s-light/cp_magic_painter/docu/prepare_images/gimp export BMP_settings.png

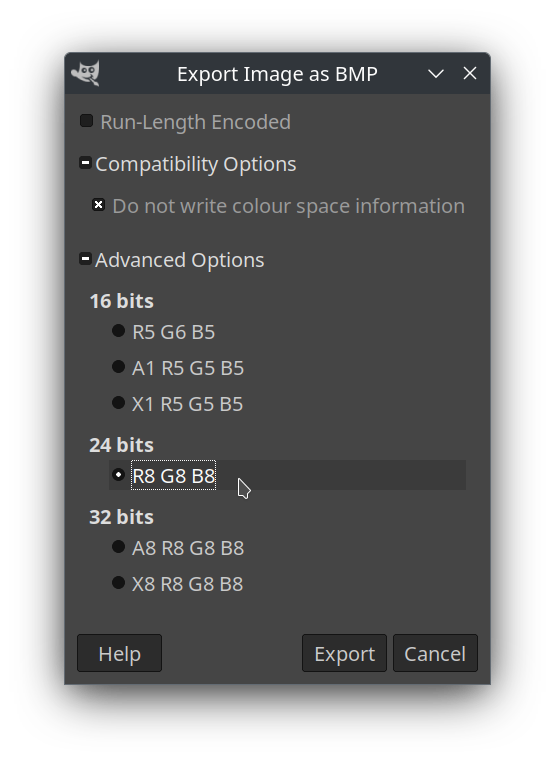
docu/prepare_images/gimp export BMP_settings.png
