s-light/cp_magic_painter/docu/prepare_images/openmoji.org candle PNG CtrClickCopy.png

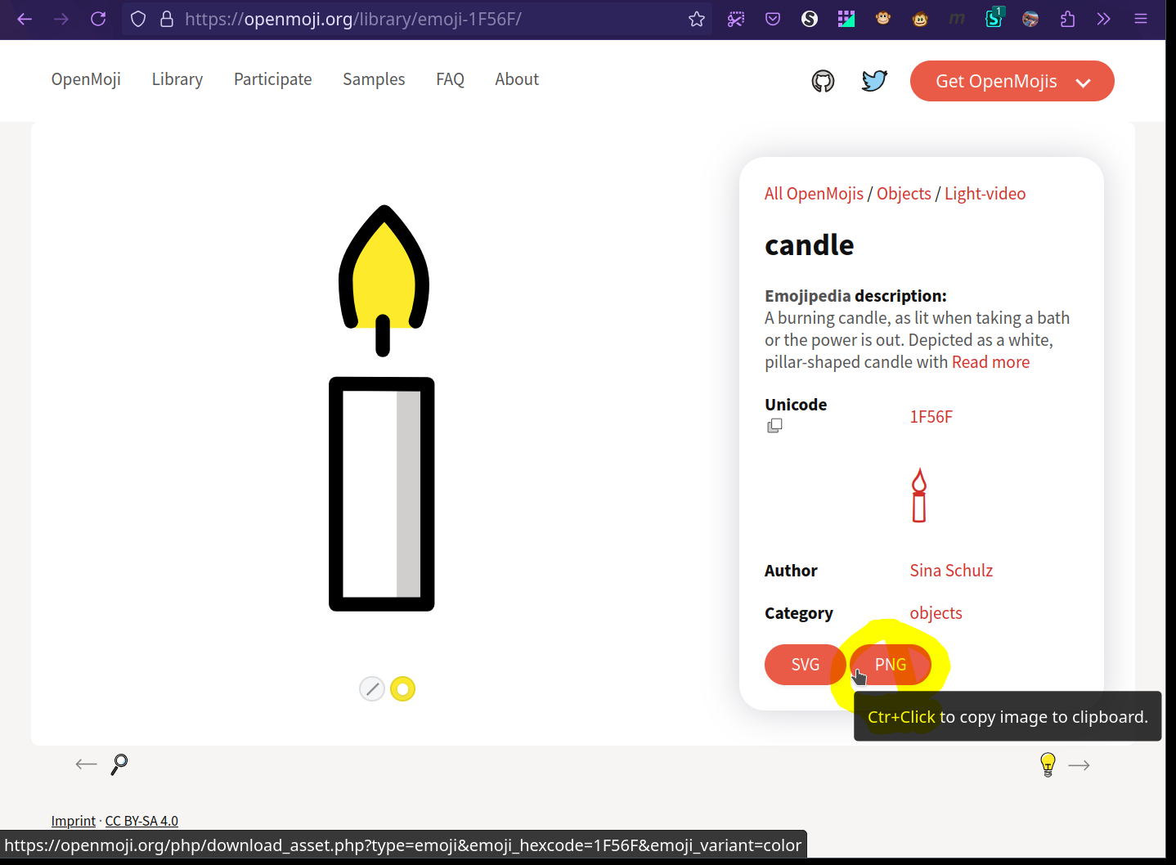
docu/prepare_images/openmoji.org candle PNG CtrClickCopy.png
