s-light/cp_magic_painter/docu/prepare_images/openmoji.org candle selected.png

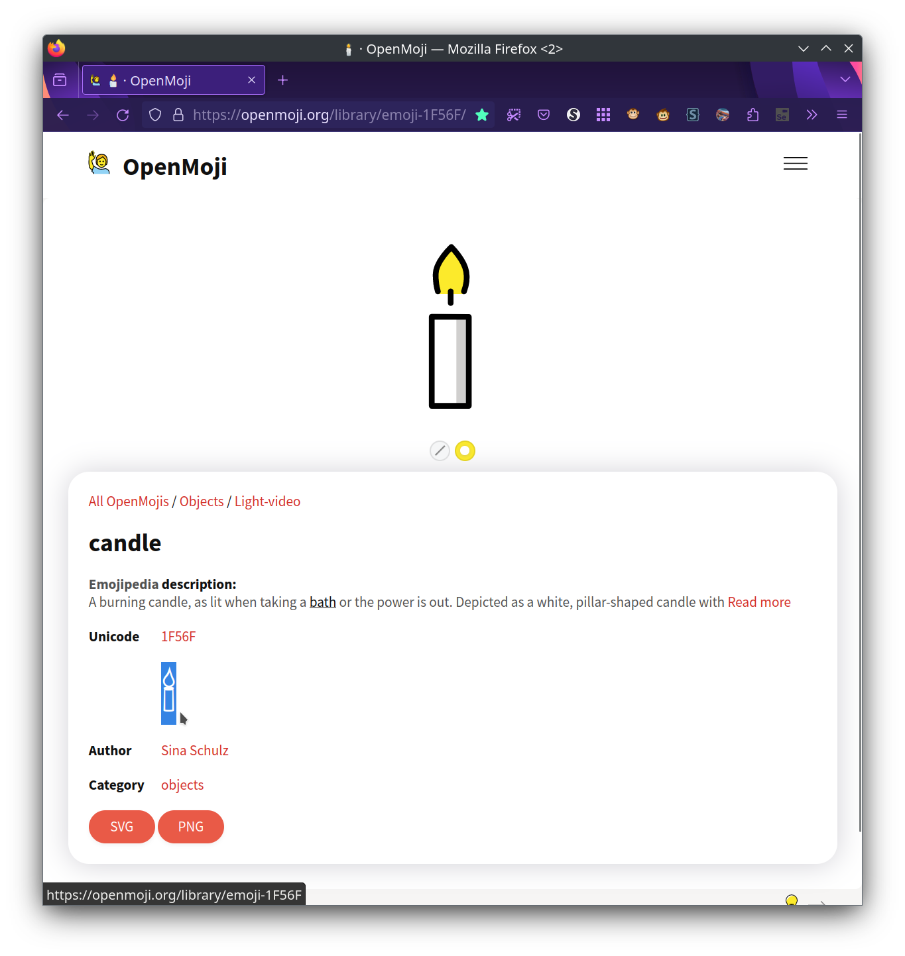
docu/prepare_images/openmoji.org candle selected.png
