s-light/cp_magic_painter/hw/pictures/20230304_v0/20230304_070338__hw.jpg

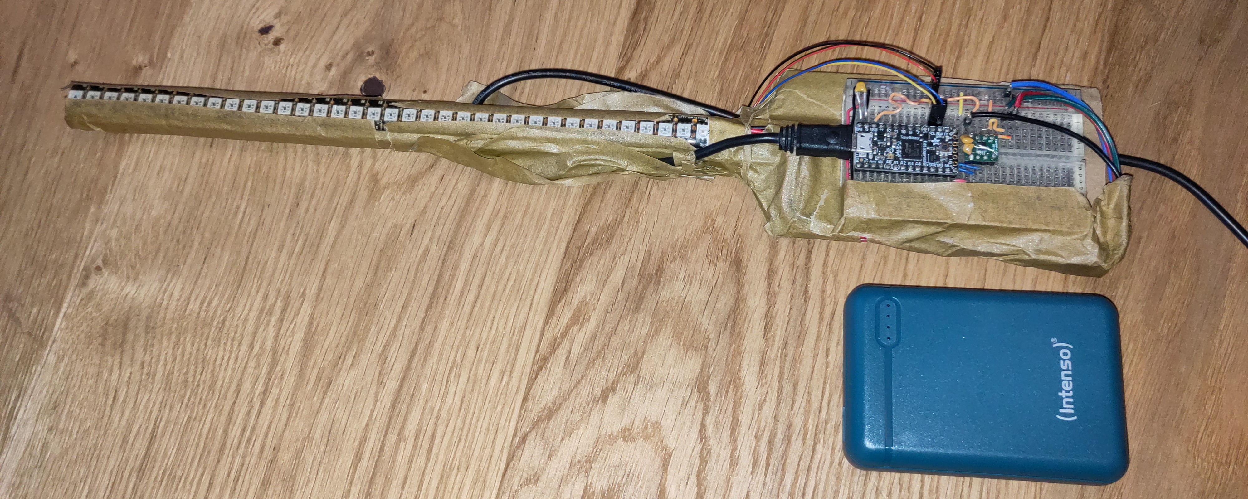
hw/pictures/20230304_v0/20230304_070338__hw.jpg
