s-light/cp_magic_painter/hw/pictures/20230304_v0/20230304_070426__crop_detail1.jpg

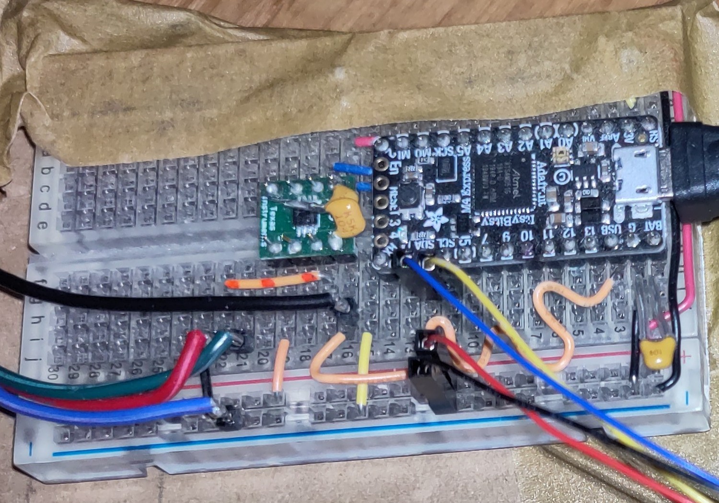
hw/pictures/20230304_v0/20230304_070426__crop_detail1.jpg
