s-light/cp_magic_painter/hw/pictures/20230304_v0/20230304_071858_DRO.jpg

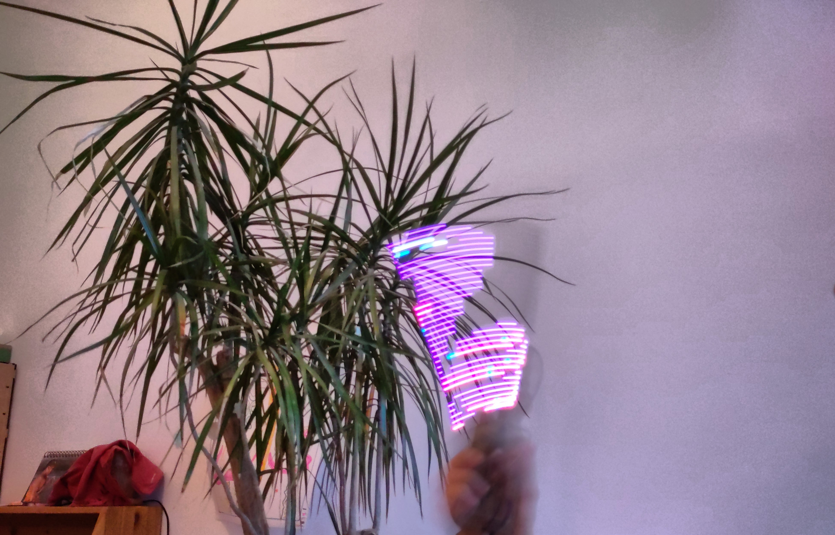
hw/pictures/20230304_v0/20230304_071858_DRO.jpg
