s-light/cp_magic_painter/hw/pictures/20230425_v1/20230422_122205.jpg

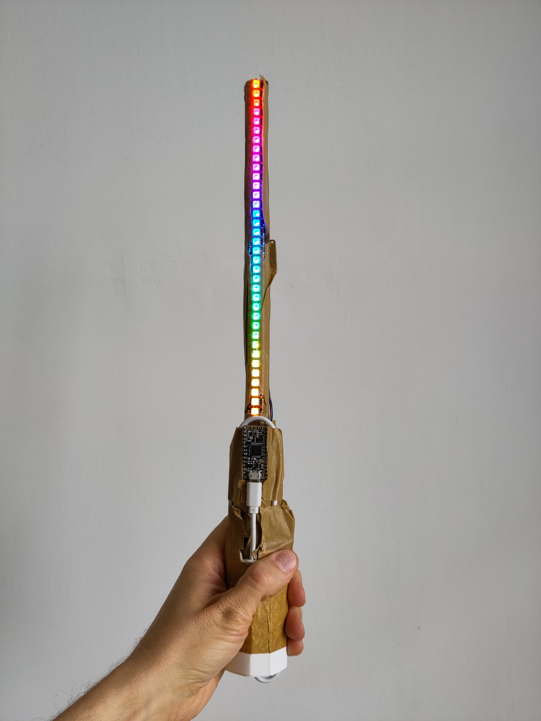
hw/pictures/20230425_v1/20230422_122205.jpg
