s-light/cp_magic_painter/hw/pictures/20230521_v2/20230628_010837.jpg

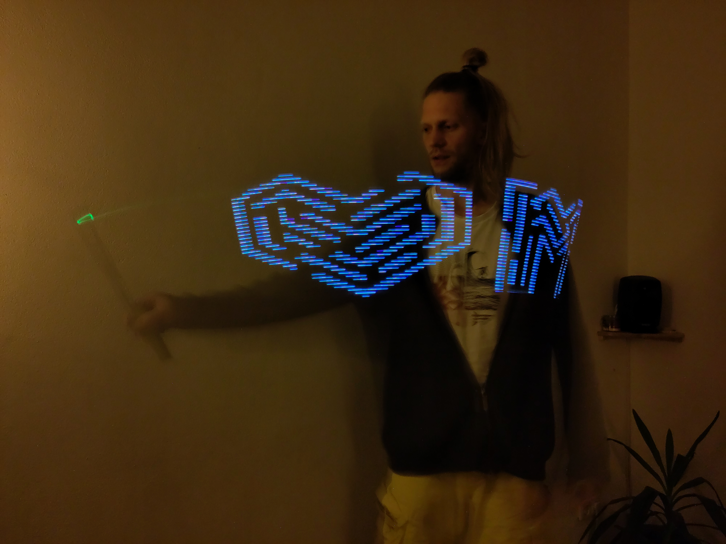
hw/pictures/20230521_v2/20230628_010837.jpg
