s-light/cp_magic_painter/hw/pictures/20230521_v2/20230628_011204.jpg

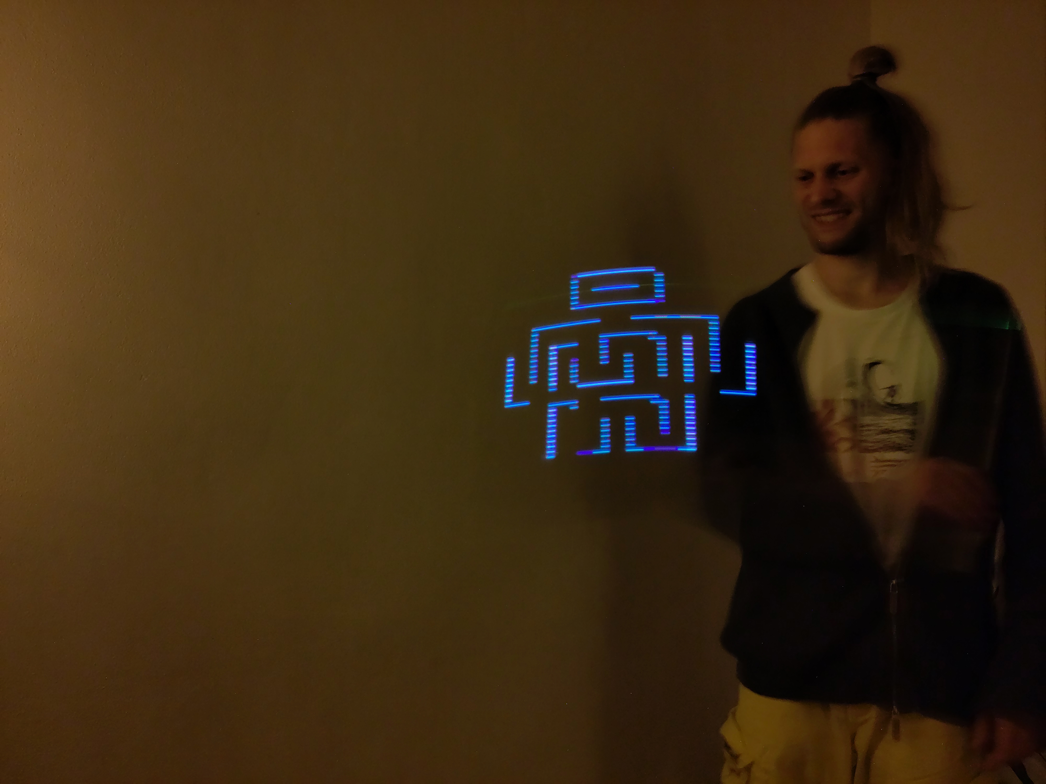
hw/pictures/20230521_v2/20230628_011204.jpg
