s-light/cp_magic_painter/hw/pictures/20230709 powerbank/20230709_113732.jpg

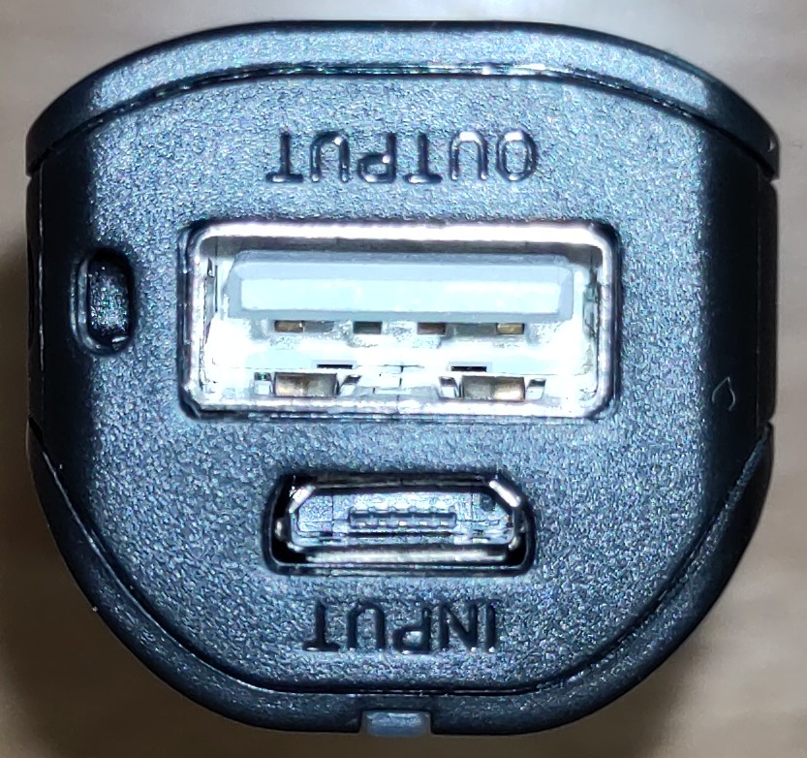
hw/pictures/20230709 powerbank/20230709_113732.jpg
