s-light/cp_magic_painter/hw/pictures/20230709 powerbank/20230709_113805.jpg

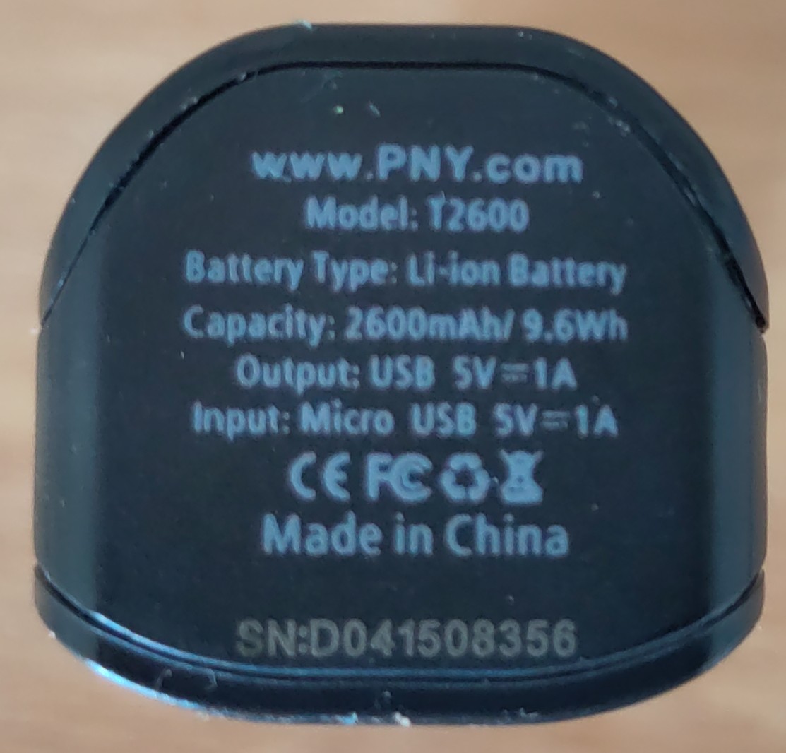
hw/pictures/20230709 powerbank/20230709_113805.jpg
