s-light/cp_magic_painter/hw/pictures/20230709 powerbank/20230709_114218.jpg

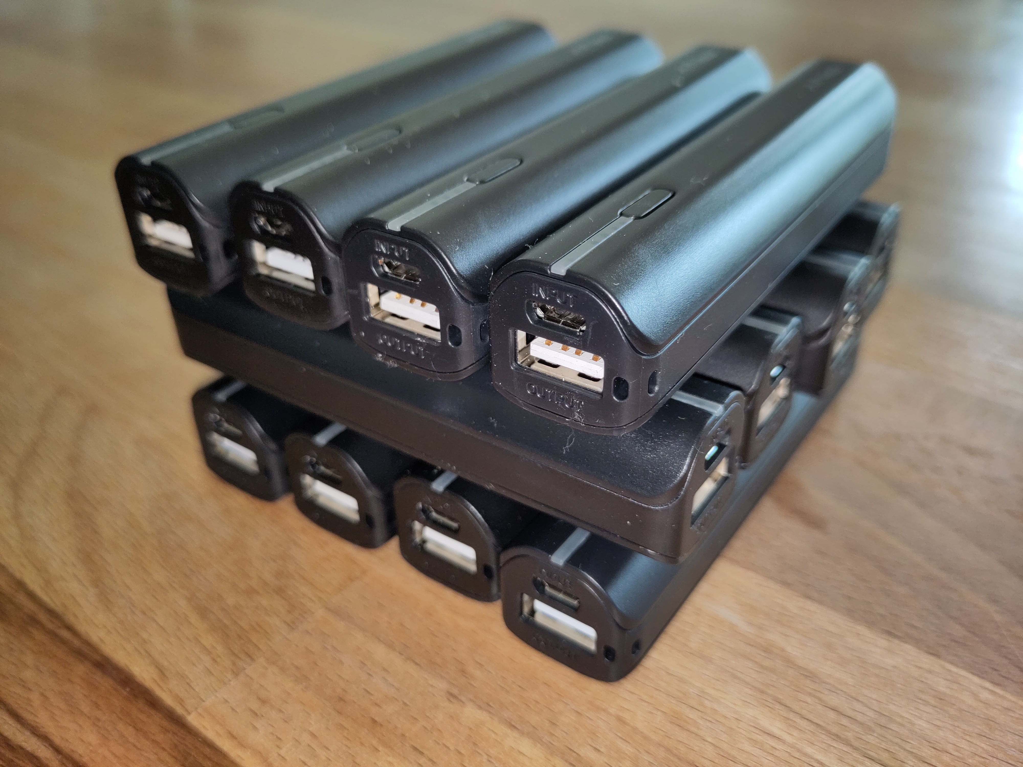
hw/pictures/20230709 powerbank/20230709_114218.jpg
