s-light/cp_magic_painter/hw/pictures/20230709 powerbank/20230726_093031.jpg

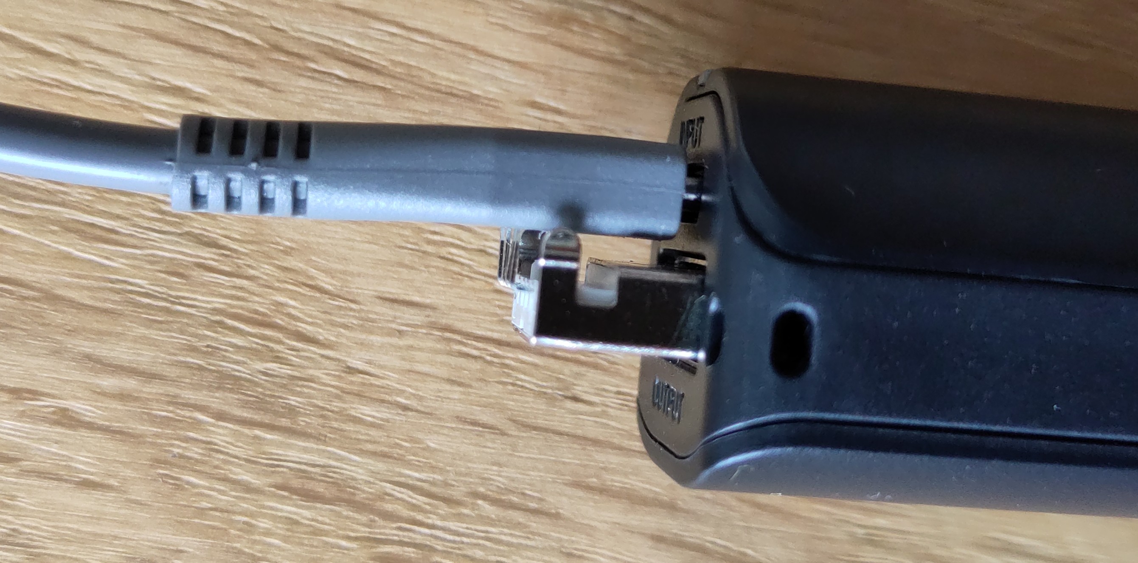
hw/pictures/20230709 powerbank/20230726_093031.jpg
