s-light/cp_magic_painter/hw/shrinktube_check.png

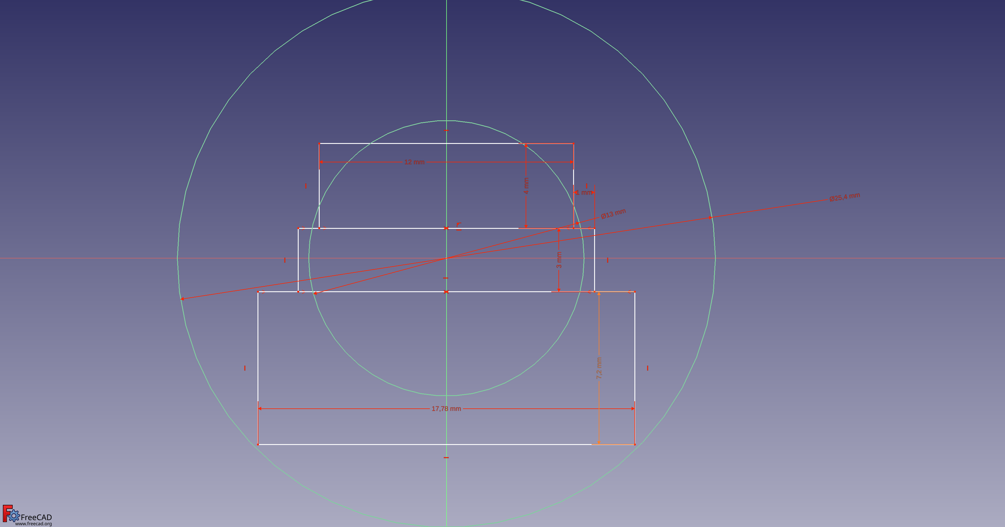
hw/shrinktube_check.png
