s-light/cp_magic_painter/hw/case/led_strip.FCStd

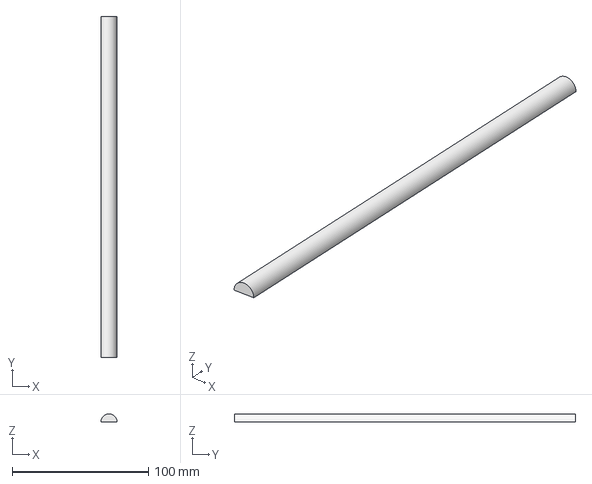
[picture p47: CAD file, 2023-09-12]
hw/case/led_strip.FCStd
12.0 x 250.0 x 6.00 mm
