s-light/cp_magic_painter/hw/case/LIS3DH.FCStd

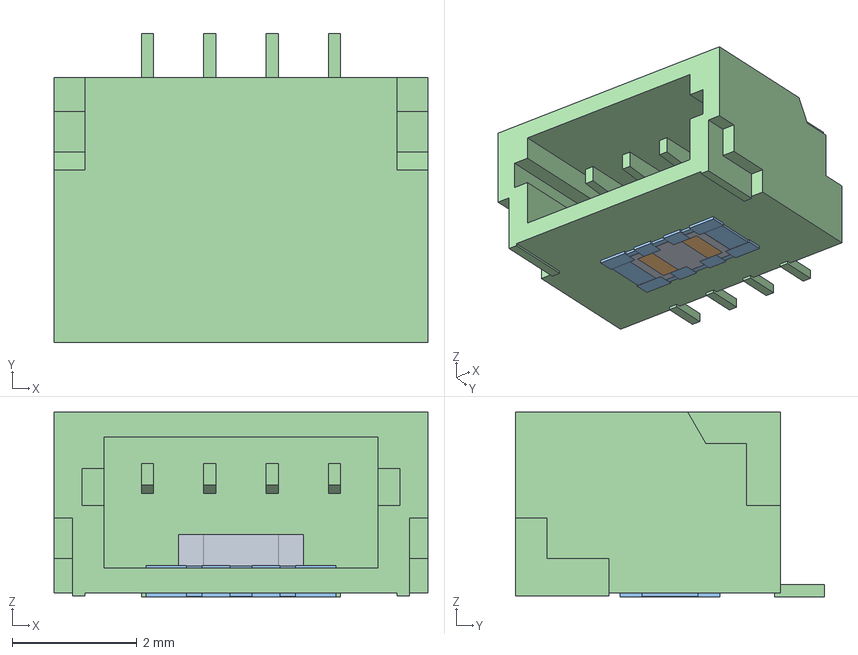
[picture p48: CAD file, 2023-09-12]
hw/case/LIS3DH.FCStd
6.00 x 4.95 x 2.96 mm
0805-NO
0603-NO
RESPACK_4X0603
JST_SH4
