s-light/cp_magic_painter/hw/case/test_LC_Interlock.FCStd

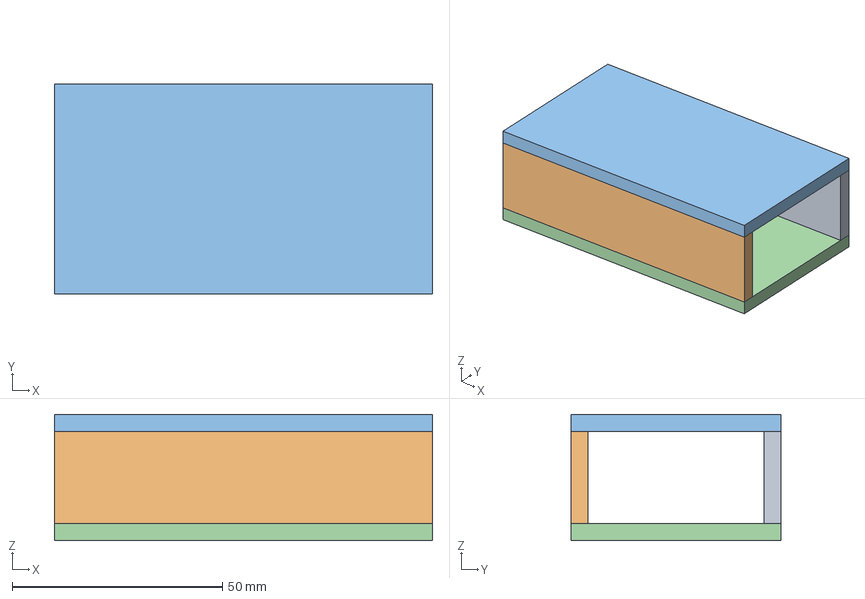
[picture p49: CAD file, 2023-08-19]
hw/case/test_LC_Interlock.FCStd
90.0 x 50.0 x 30.0 mm
face_panel_tab
behind_panel_tab
top_panel_tab
bottom_panel_tab
