s-light/cp_magic_painter/hw/case/case.FCStd

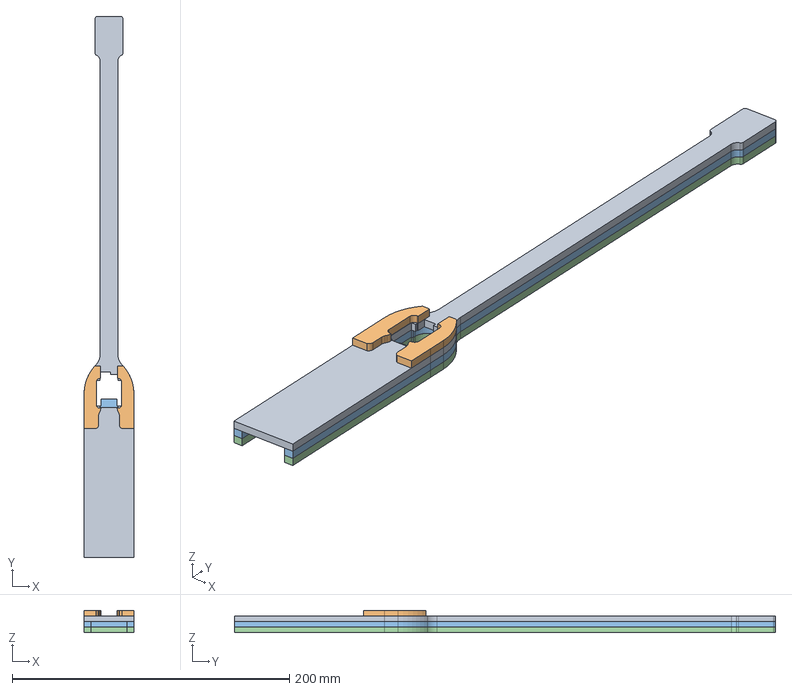
[picture p50: CAD file, 2023-08-08]
hw/case/case.FCStd
36.0 x 390.0 x 16.0 mm
case_layer_0
case_layer_-1 x 2
case_layer_1
case_layer_2
