s-light/cp_magic_painter/hw/case/usb_plug__original.FCStd

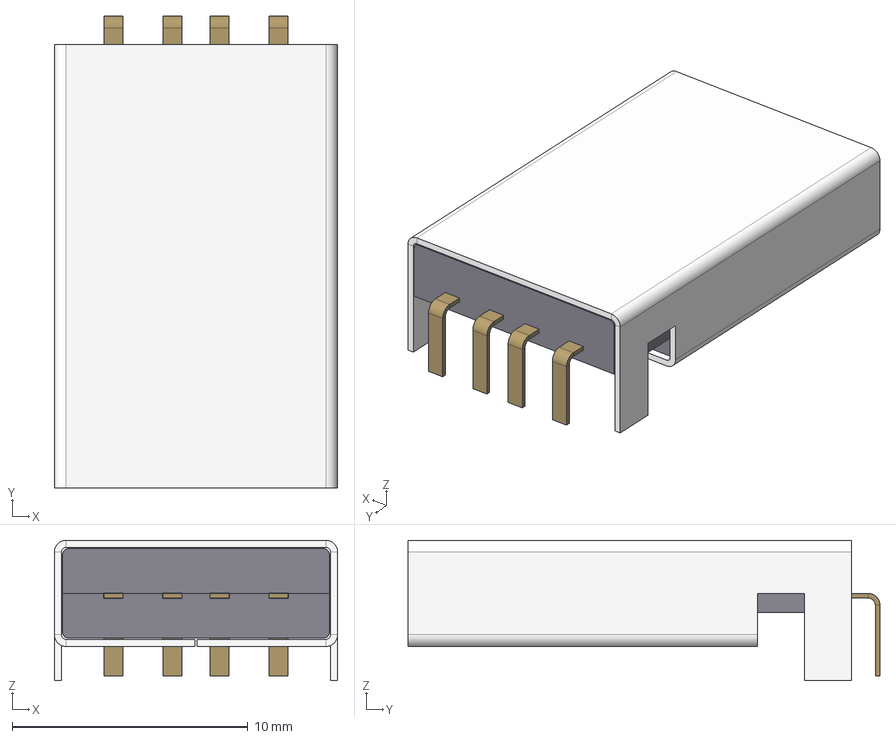
[picture p51: CAD file, 2023-08-08]
hw/case/usb_plug__original.FCStd
12.0 x 20.0 x 5.95 mm
pin_Body x 4
fill_Body
