s-light/cp_magic_painter/docu/build_hw/01 prepare wood/20240919_201957 case - usb slide in - glued.jpg

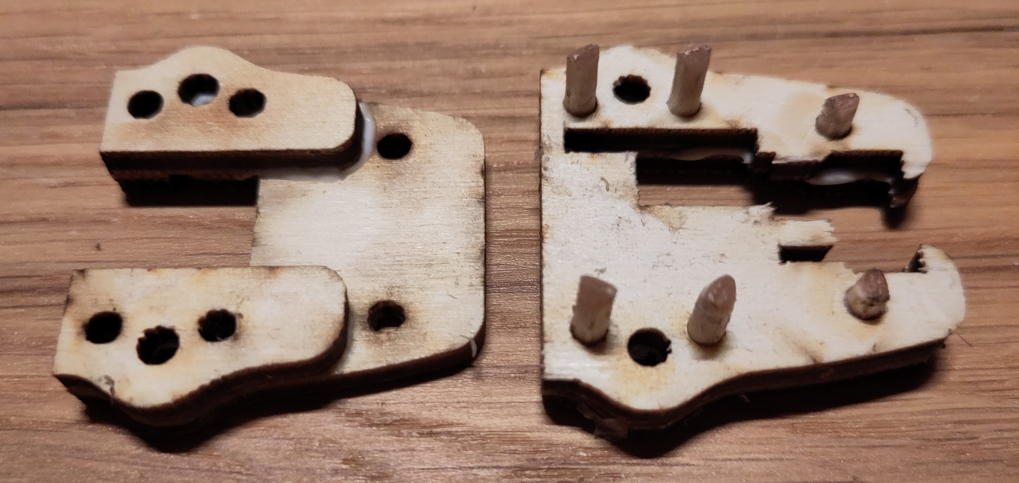
docu/build_hw/01 prepare wood/20240919_201957 case - usb slide in - glued.jpg
