s-light/cp_magic_painter/docu/build_hw/02 solder electronics/20230915_122823.jpg

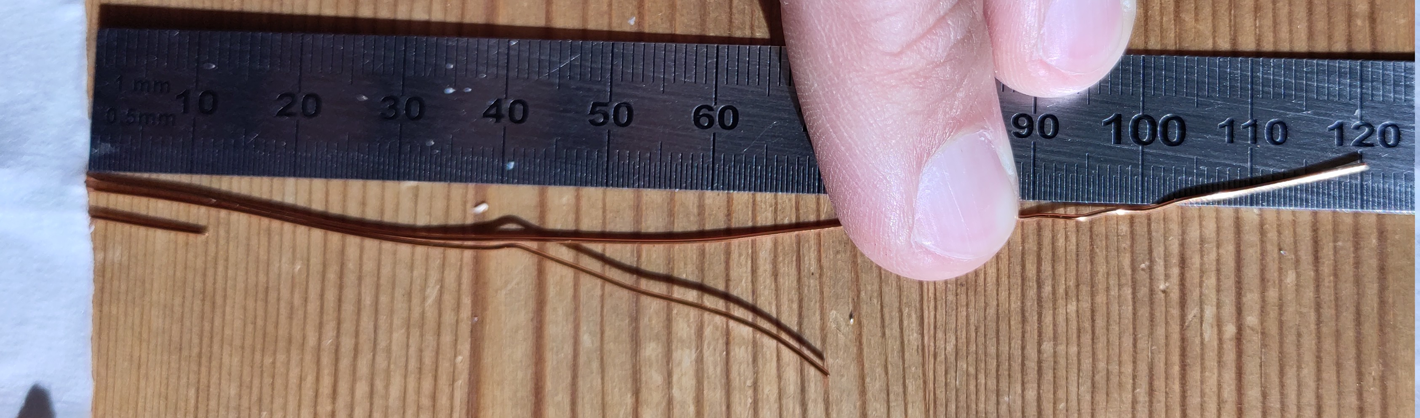
docu/build_hw/02 solder electronics/20230915_122823.jpg
