s-light/cp_magic_painter/docu/build_hw/02 solder electronics/20240821_113141 wires power.jpg

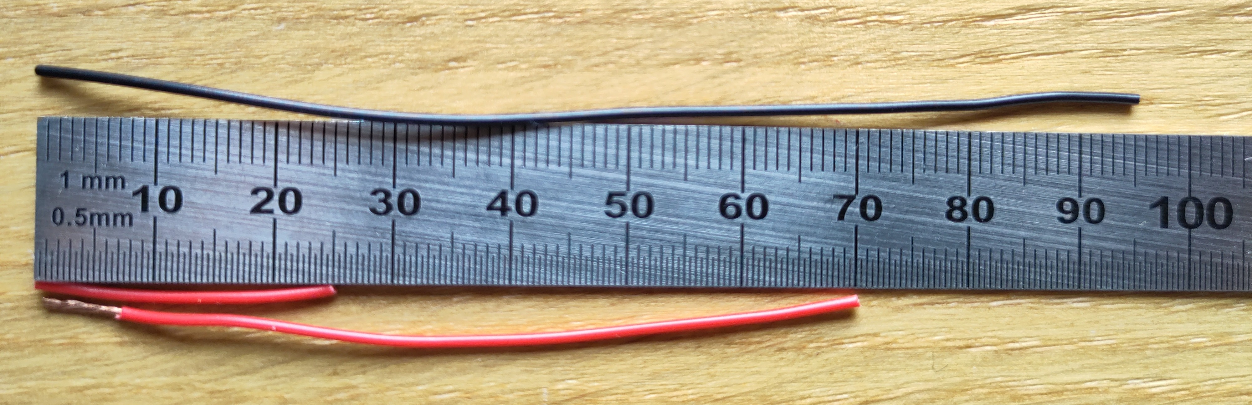
docu/build_hw/02 solder electronics/20240821_113141 wires power.jpg
