s-light/cp_magic_painter/docu/build_hw/04 build/20241002_164916 shrink-tube cover .jpg

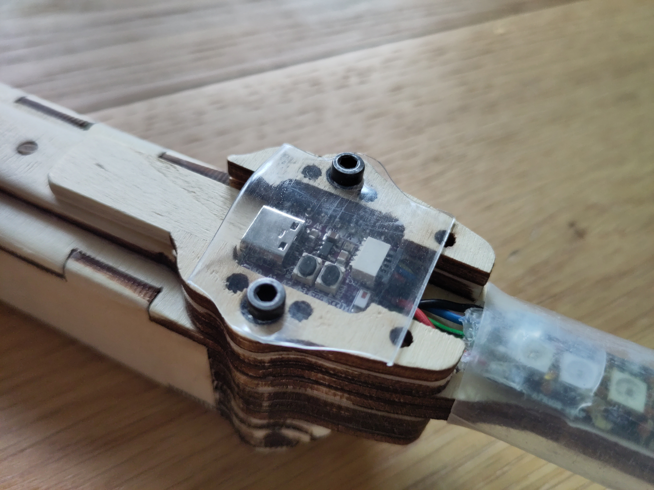
docu/build_hw/04 build/20241002_164916 shrink-tube cover .jpg
