s-light/cp_magic_painter/hw/case/case_assembly.png

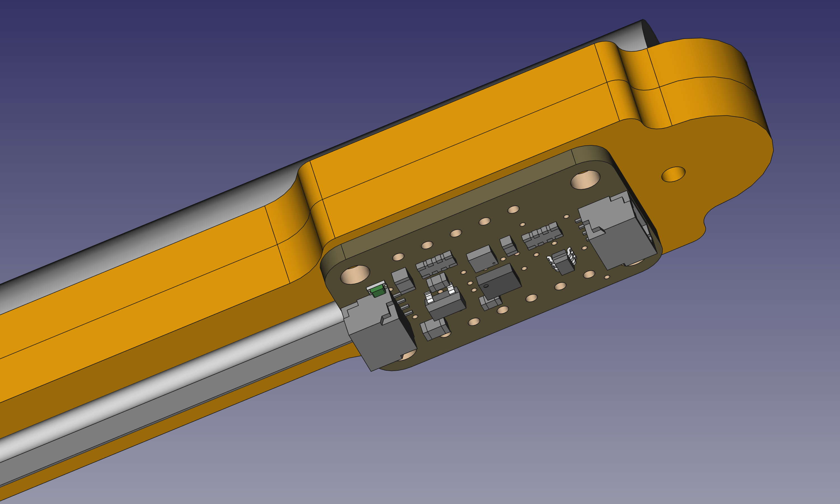
hw/case/case_assembly.png
