s-light/cp_magic_painter/hw/case/case_assembly_screenshots/detail_back_inside.png

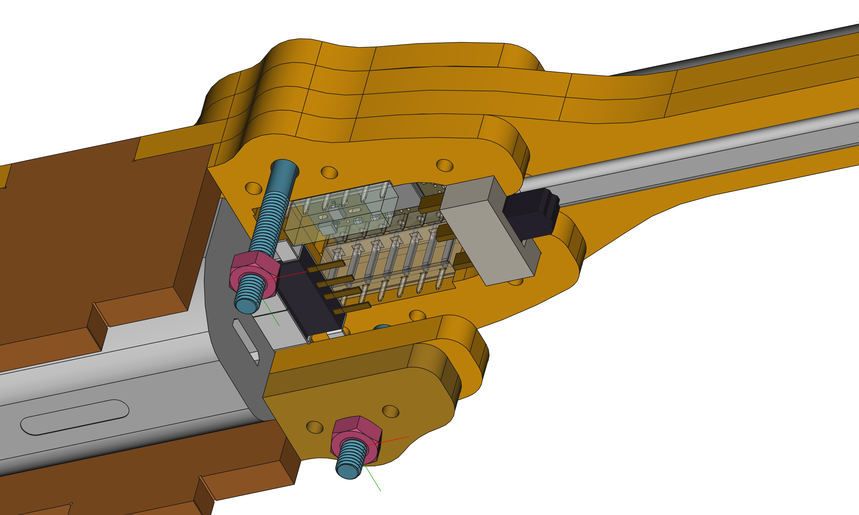
hw/case/case_assembly_screenshots/detail_back_inside.png
