s-light/cp_magic_painter/hw/case/case_assembly_screenshots/detail_front.png

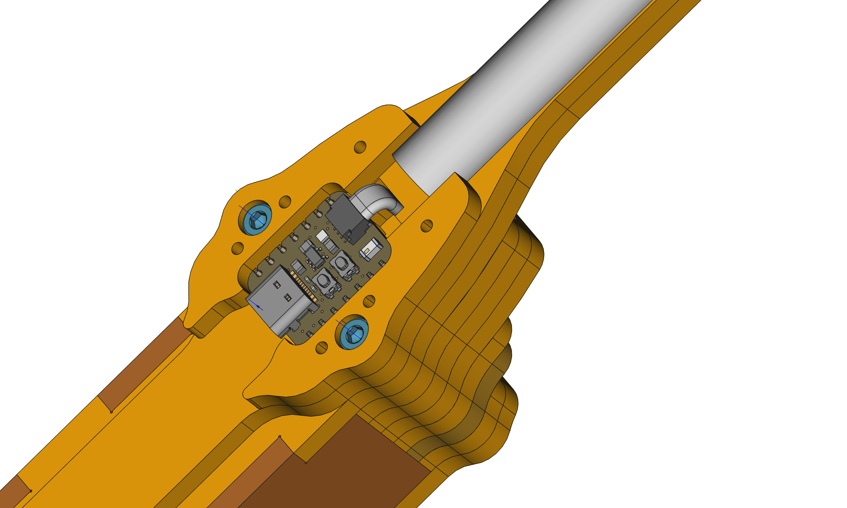
hw/case/case_assembly_screenshots/detail_front.png
