s-light/cp_magic_painter/hw/case/case_assembly_screenshots/detail_top_sensor.png

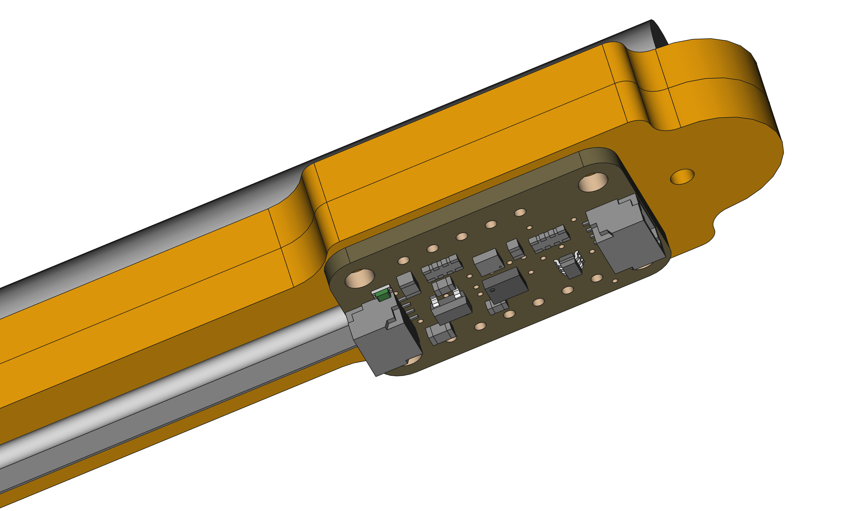
hw/case/case_assembly_screenshots/detail_top_sensor.png
