s-light/cp_magic_painter/cp_tests/lis3dh/shake_test0/lis3dh_plot__export_shake_mod.png

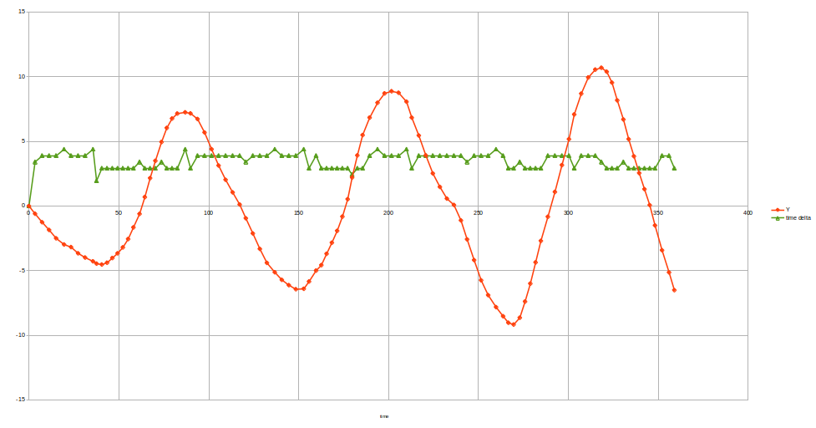
cp_tests/lis3dh/shake_test0/lis3dh_plot__export_shake_mod.png
