s-light/cp_magic_painter/cp_tests/lis3dh/shake_test1/lis3dh_plot_with_shake_detection__export.png

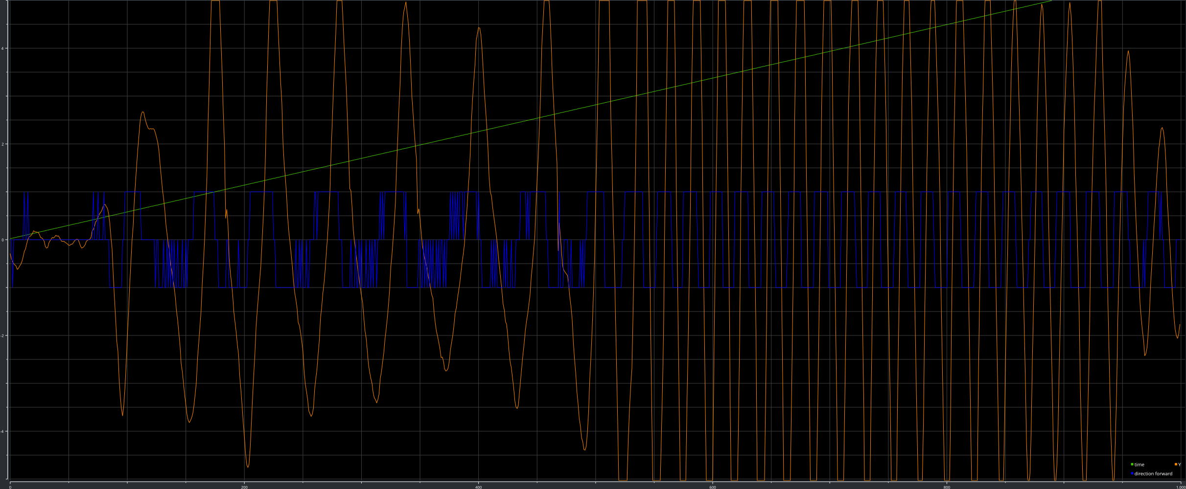
cp_tests/lis3dh/shake_test1/lis3dh_plot_with_shake_detection__export.png
