s-light/cp_magic_painter/cp_tests/lis3dh/shake_test2/lis3dh_plot_with_shake_detection.png

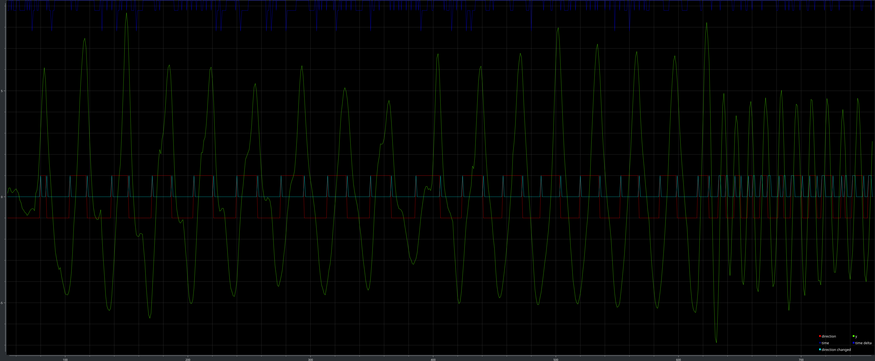
cp_tests/lis3dh/shake_test2/lis3dh_plot_with_shake_detection.png
