s-light/cp_magic_painter/docu/build_hw/03 test electronics/20230917_012738.jpg

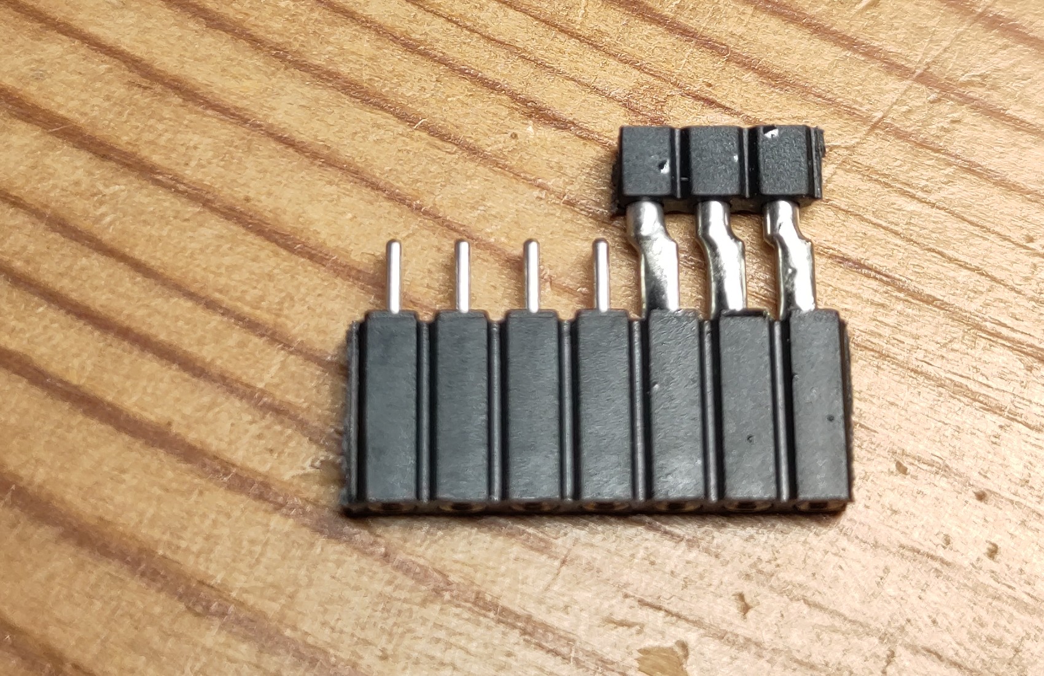
docu/build_hw/03 test electronics/20230917_012738.jpg
