s-light/cp_magic_painter/hw/pictures/20230506_size_tests/20230511_103406.jpg

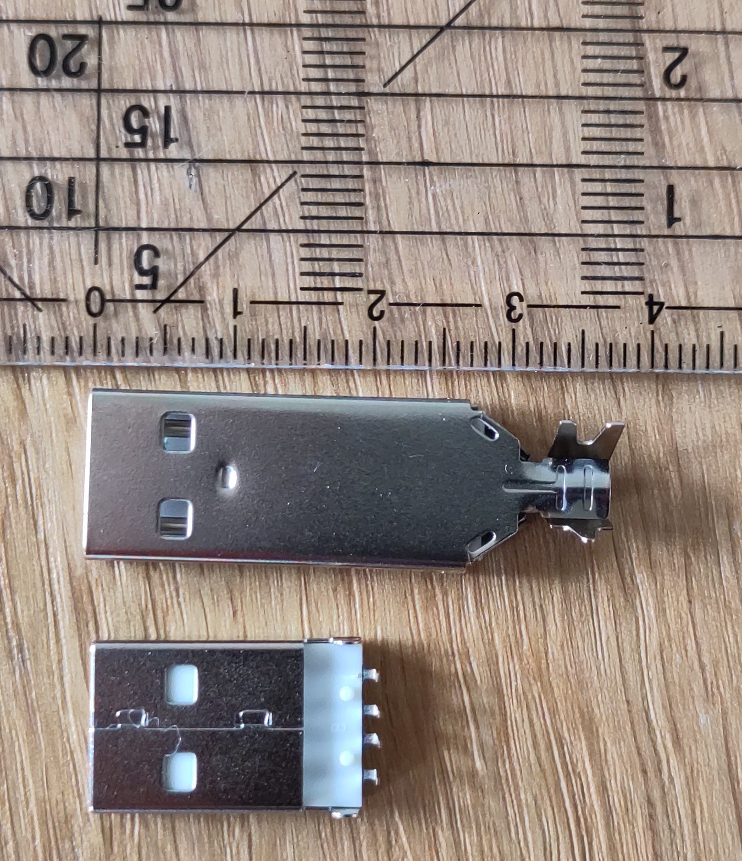
hw/pictures/20230506_size_tests/20230511_103406.jpg
