s-light/cp_magic_painter/hw/pictures/20230512_powerbank_test/20230512_185331.jpg

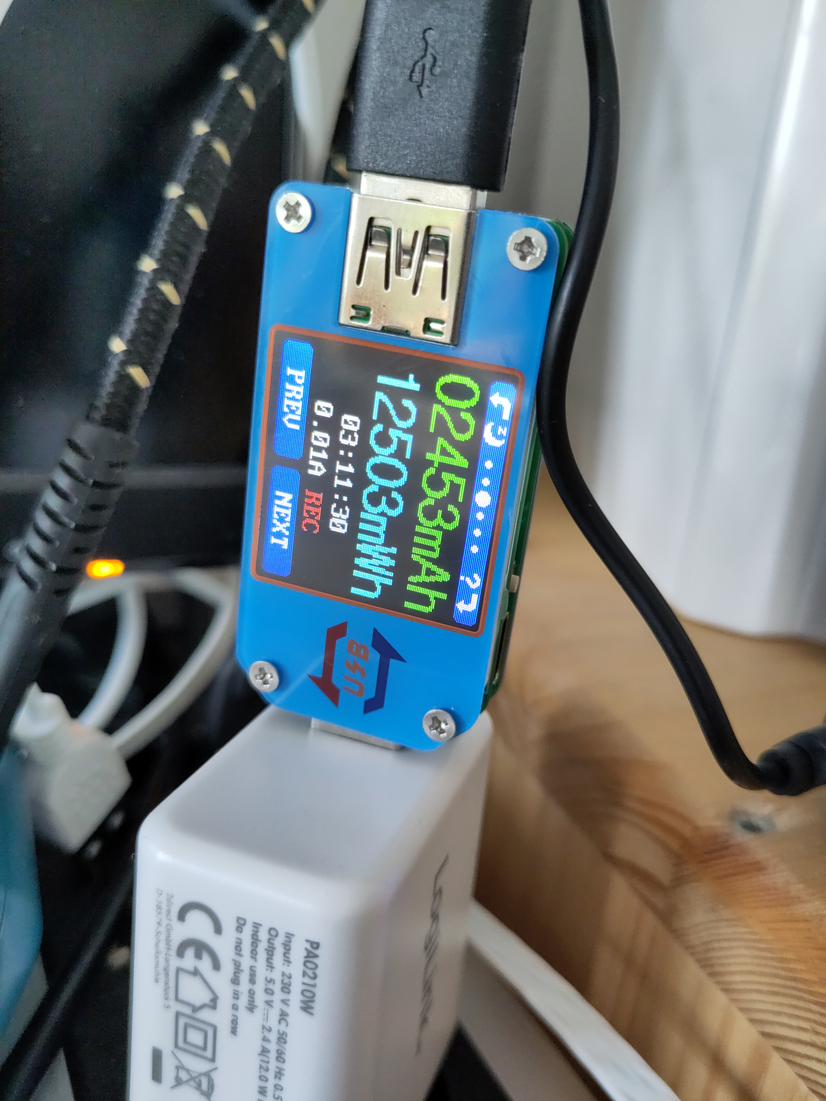
hw/pictures/20230512_powerbank_test/20230512_185331.jpg
