s-light/cp_magic_painter/CIRCUITPY_disc/src/rgblamp.py

# SPDX-FileCopyrightText: 2018 Kattni Rembor for Adafruit Industries
# SPDX-License-Identifier: MIT
# https://learn.adafruit.com/circuitpython-essentials/circuitpython-dotstar

"""RGB Lamp"""
import os
import time
import math

import board
import displayio
from rainbowio import colorwheel
import adafruit_fancyled.adafruit_fancyled as fancy
import adafruit_dotstar

from adafruit_fancyled.adafruit_fancyled import CHSV, CRGB

import socketpool
import wifi
import adafruit_ntp
import rtc

import displayio
import terminalio
from adafruit_bitmap_font import bitmap_font
from adafruit_display_text import label

import helper

from mode_base import ModeBaseClass

from gesture_detector import (
    UNKNOWN,
    REST,
    REST_HORIZONTAL,
    REST_VERTICAL,
    TILT_LEFT,
    TILT_RIGHT,
    TAB_X,
    TAB_Y,
    TAB_Z,
    DIRECTION_CHANGED,
    SHAKE_X,
    SHAKE_Y,
    SHAKE_Z,
)


class RGBLamp(ModeBaseClass):
    __name__ = "RGBLamp"

    config_defaults = {
        "RGBLamp": {
            "mode": "nightlight",
            "brightness": 0.02,
            # duration for full fade from 0 to 1 in seconds
            # "brightness_fade_duration": 10,
            # effect duration in seconds (default 10min)
            "effect_duration": 10 * 60,
            "effect_active": True,
            # https://learn.adafruit.com/fancyled-library-for-circuitpython/colors#hsv-colors-2981215
            # only specifying Hue → purple
            "color_range": {
                "min": CHSV(0.50),
                "max": CHSV(0.9),
            },
            "extra_effects": {
                # "y_to_brightness":False,
                "y_to_brightness": (0.2, 0.7),
            },
        },
    }

    brightness_map = [
        # in , out
        (0.0, 0.02),
        # in this range use brightness_mask
        (0.5, 0.02),
        (0.7, 0.1),
        (1.0, 0.7),
    ]
    # brightness_map_mask = [
    #     (0.0, 1),
    #     (1.0, 1),
    # ]

    def __init__(self, *, config={}, print_fn, accel_sensor):
        super(RGBLamp, self).__init__(config=config, print_fn=print_fn)
        self.print = print
        self.accel_sensor = accel_sensor

        self._brightness = 0.0
        self.brightness_mapped = 0.0

        print(42 * "*")
        print("RGBLamp")
        print(42 * "*")

        self.config_extend_with_defaults(defaults=self.config_defaults)
        # self.print(self.config)
        # print(self.__class__, "config extended:")
        self.num_pixels = self.config["hw"]["pixel_count"]

        # effect base
        # print("    prepare effect")
        self.effect_active = self.config["RGBLamp"]["effect_active"]
        self.effect_duration = self.config["RGBLamp"]["effect_duration"]
        self.effect_start_cycle()
        self._offset = 0

        # print("    prepare color")
        self.color_range = self.config["RGBLamp"]["color_range"]
        self.hue_min = self.color_range["min"].hue
        self.hue_max = self.color_range["max"].hue
        self.hue_center = helper.map_01_to(0.5, self.hue_min, self.hue_max)

        # effect plasma
        self._contrast = 1
        self._contrast_min = 0.5
        self._contrast_max = 1.0
        self.animation_contrast = 0.99

        # extra_effects
        self.fx__y_to_brightness = self.config["RGBLamp"]["extra_effects"][
            "y_to_brightness"
        ]

        # print("    prepare brightness")
        # brightness
        self.brightness_map_mask = [
            # in , out
            #      led_count on
            (0.0, 1),
            (0.3, ((0.3 * 2 * 10) + 1)),  # 7
            (0.5, self.num_pixels),
            (1.0, self.num_pixels),
        ]
        self.mask_pixel_active_count = self.num_pixels
        self.mask_pixel_black_count = self.num_pixels - self.mask_pixel_active_count

        self.setup_rtc()
        self.setup_display()

        # print("    spi_init")
        self.spi_init()

        # self.print("brightness mapping test:")
        # for value in range(0, 105, 5):
        #     self.brightness = value / 100

        self.brightness = self.config["RGBLamp"]["brightness"]

        # print("    main_loop")
        # run animation rendering one time.
        self.main_loop()

        # print("    spi_deinit")
        self.spi_deinit()
        # print("    spi_deinit done.")

        # we need to to this as last action -
        # otherwise we get into dependency hell as not all things shown in status line are initialized..
        self.print = print_fn
        print("rgblamp init done.")

    ##########################################
    # properties

    @property
    def brightness(self):
        # return ModeBaseClass.brightness
        return self._brightness

    @brightness.setter
    def brightness(self, value):
        # super(POVPainter, self).brightness = value
        # https://github.com/python/cpython/issues/59170#issuecomment-1093581234
        # we need a workaround..
        # ModeBaseClass.brightness = value
        value = helper.limit(value, 0.0, 1.0)
        self._brightness = value
        # Remap brightness from 0.0-1.0 to brightness_range.
        # self.print("brightness - self.brightness:", self.brightness)
        # test = helper.map_01_to(value, 0.0, 0.7)
        # self.print("brightness - map_range:", test)
        # self.print("brightness - test:", test)

        value_mapped = helper.multi_map(value, self.brightness_map)
        # self.pixels.brightness = value_mapped
        self.brightness_mapped = value_mapped

        # mask things
        self.mask_pixel_active_count = int(
            helper.multi_map(value, self.brightness_map_mask)
        )
        self.mask_pixel_black_count = self.num_pixels - self.mask_pixel_active_count
        # self.print("num_pixels", self.num_pixels)
        # self.print("mask_pixel_active_count", self.mask_pixel_active_count)
        # self.print("mask_pixel_black_count", self.mask_pixel_black_count)
        # if self.mask_pixel_black_count > 0:
        self.mask_black_array = [(0, 0, 0)] * (self.mask_pixel_black_count)
        # self.print("mask_black_array", self.mask_black_array)

        # self.print(
        #     "brightness - "
        #     "input:{: > 6.2f}  "
        #     "mask:{: > 4}  "
        #     "mapped:{: > 7.2f}  "
        #     "".format(
        #         value,
        #         self.mask_pixel_active_count,
        #         value_mapped,
        #     )
        # )

    # @property
    # def animation_contrast(self):
    #     """Get animation_contrast value."""
    #     return self._contrast

    # @animation_contrast.setter
    # def animation_contrast(self, value):
    #     """Set animation_contrast value."""
    #     self._contrast = value
    #     # self._contrast_min = self._contrast - 0.5
    #     # self._contrast_max = self._contrast + 0.5
    #     self._contrast_min = 1 - self._contrast
    #     self._contrast_max = 1

    ##########################################
    # hw

    def spi_init(self):
        # deactivate internal displays...
        # displayio.release_displays()
        self.pixels = adafruit_dotstar.DotStar(
            helper.get_pin(
                config=self.config, bus_name="pixel_spi_pins", pin_name="clock"
            ),
            helper.get_pin(
                config=self.config, bus_name="pixel_spi_pins", pin_name="data"
            ),
            self.num_pixels,
            # brightness=0.01,
            auto_write=False,
        )

        self.main_loop()

    def spi_deinit(self):
        self.pixels.deinit()

    # ~~~~~~~~~~~~~~~~~~~~~~~~~~~~~~~~~~~~~~~~~~
    # display time

    def setup_rtc(self):
        # Get wifi AP credentials from a settings.toml file
        wifi_ssid = os.getenv("CIRCUITPY_WIFI_SSID")
        wifi_password = os.getenv("CIRCUITPY_WIFI_PASSWORD")
        if wifi_ssid is None:
            print("WiFi credentials are kept in settings.toml, please add them there!")
            raise ValueError("SSID not found in environment variables")

        try:
            wifi.radio.connect(wifi_ssid, wifi_password)
        except ConnectionError:
            print("Failed to connect to WiFi with provided credentials")
            raise

        pool = socketpool.SocketPool(wifi.radio)
        ntp = adafruit_ntp.NTP(pool, tz_offset=0, cache_seconds=3600)

        # NOTE: This changes the system time so make sure you aren't assuming that time
        # doesn't jump.
        rtc.RTC().datetime = ntp.datetime

    def setup_display(self):
        # font = terminalio.FONT
        font = bitmap_font.load_font("/Overlock-Bold-40.bdf")
        current = time.localtime()
        time_display = "{:02d}:{:02d}:{:02d}".format(
            current.tm_hour, current.tm_min, current.tm_sec
        )
        self.text_area = label.Label(font, text=time_display)

        display = board.DISPLAY
        # Make the display context
        splash = displayio.Group()
        display.root_group = splash

        FONTSCALE = 1

        # scale and center
        text_width = self.text_area.bounding_box[2] * FONTSCALE
        text_group = displayio.Group(
            scale=FONTSCALE,
            x=display.width // 2 - text_width // 2,
            y=display.height // 2,
        )
        text_group.append(self.text_area)  # Subgroup for text scaling
        splash.append(text_group)

    # ~~~~~~~~~~~~~~~~~~~~~~~~~~~~~~~~~~~~~~~~~~
    # user interface

    def handle_user_input_touch(self, event):
        if event.touch.rose:
            # self.print("RGBLamp - handle_user_input: ", touch_id)
            if event.touch_id == 0:
                self.brightness += 0.05
            elif event.touch_id == 1:
                self.brightness -= 0.05
            elif event.touch_id == 2:
                self.brightness = 0.01
            self.print("(touch ", event.touch_id, ") brightness", self.brightness)
            # self.print("pixels.brightness", self.pixels.brightness)
        self.button_event.pressed
        if event.touch.rose:
            # self.print("RGBLamp - handle_user_input: ", touch_id)
            if event.touch_id == 0:
                self.brightness += 0.05
            elif event.touch_id == 1:
                self.brightness -= 0.05
            elif event.touch_id == 2:
                self.brightness = 0.01
            self.print("(touch ", event.touch_id, ") brightness", self.brightness)
            # self.print("pixels.brightness", self.pixels.brightness)

    def handle_user_input_button(self, event):
        self.print("RGBLamp - handle_user_input_button: ", event)
        if event.pressed:
            if event.key_number == 1:
                self.hue_min += 0.025
                self.hue_max += 0.025
                # wrap around
                # not really needed as teh HSV conversion takes care of this..
                # if self.hue_min > 1.0:
                #     self.hue_min -= 1.0
                # if self.hue_max > 1.0:
                #     self.hue_max -= 1.0
            elif event.key_number == 2:
                self.hue_min -= 0.025
                self.hue_max -= 0.025
                # if self.hue_min < 1.0:
                #     self.hue_min += 1.0
                # if self.hue_max < 1.0:
                #     self.hue_max += 1.0
            elif event.key_number == 3:
                self.hue_min = self.color_range["min"].hue
                self.hue_max = self.color_range["max"].hue

    def handle_gesture(self, event):
        if event.gesture == TILT_RIGHT:
            self.brightness += 0.1
        elif event.gesture == TILT_LEFT:
            self.brightness -= 0.1

    # statusline_template = "color: {color} "
    statusline_template = "color: hue_min {hue_min:>4.3f}, hue_max {hue_max:>4.3f} "

    def statusline_fn(self):
        """
        Generate statusline.

        NO prints in this function!!
        (leads to infinity loops..)
        """

        statusline = self.statusline_template.format(
            # color=self.color_range,
            hue_min=self.hue_min,
            hue_max=self.hue_max,
        )

        return statusline

    # ~~~~~~~~~~~~~~~~~~~~~~~~~~~~~~~~~~~~~~~~~~
    # animation functions

    def effect_start_cycle(self):
        self.print("effect_start_cycle")
        self.effect_start_ts = time.monotonic()
        self.effect_end_ts = self.effect_start_ts + self.effect_duration

    def offset_update(self):
        # stop_ts animation if  brightness is to low / only a view LEDs are on..
        if self.effect_active and self.brightness > 0.5:
            if time.monotonic() >= (self.effect_start_ts + self.effect_duration):
                self.effect_start_cycle()
            self._offset = helper.map_to_01(
                time.monotonic(), self.effect_start_ts, self.effect_end_ts
            )

    def handle_brightness_mask(self):
        if self.mask_pixel_black_count:
            self.pixels[0 : self.mask_pixel_black_count] = self.mask_black_array

    def nightlight_update(self):
        self.pixels.fill(self.color_range["min"].pack())
        # self.pixels.fill(0)
        # self.pixels[-1] = (255, 0, 255)
        # self.pixels[-2] = (255, 0, 255)
        # self.pixels[-2] = (0, 0, 255)
        # self.pixels[-3] = (255, 0, 0)

    def rainbow_update(self):
        """based on CircuitPython Essentials DotStar example"""

        if self.hue > 1.0:
            self.hue = 0.0
        else:
            self.hue += 0.001

        for i in range(self.num_pixels):
            pixel_pos = helper.map_to_01(i, 0, self.num_pixels)
            color = CHSV(self.hue + pixel_pos)
            # handle gamma and global brightness
            color_rgb = fancy.gamma_adjust(color, brightness=self.brightness_mapped)
            self.pixels[i] = color_rgb.pack()

    def plasma_update(self):
        """simple plasma animation."""
        # mostly inspired by
        # https://www.bidouille.org/prog/plasma
        # extracted from magic_crystal_animation
        plasma_offset = helper.map_01_to(self._offset, 0.0, (math.pi * 30))
        for i in range(self.num_pixels):
            col = 0.0
            row = helper.map_range(
                i,
                0,
                self.num_pixels - 1,
                # 0, 1.0
                -0.5,
                0.5,
            )

            # moving rings
            cx = col + 0.5 * math.sin(plasma_offset / 5)
            cy = row + 0.5 * math.cos(plasma_offset / 3)
            value = math.sin(math.sqrt(100 * (cx * cx + cy * cy) + 1) + plasma_offset)
            # mapping
            contrast = helper.map_range(
                value, -1, 1, self._contrast_min, self._contrast_max
            )
            hue = helper.map_range(value, -1, 1, self.hue_min, self.hue_max)
            # map to color
            # color = fancy.CHSV(hue, v=contrast)
            color = fancy.CHSV(hue)
            # handle gamma and global brightness
            color_rgb = fancy.gamma_adjust(color, brightness=self.brightness_mapped)
            self.pixels[i] = color_rgb.pack()

    def fx_extra_update(self):
        # map movement to brightness
        if self.fx__y_to_brightness:
            accel_y = self.accel_sensor.acceleration[1]
            self.brightness = helper.map_range(
                abs(accel_y),
                20,
                0.2,
                self.fx__y_to_brightness[0],
                self.fx__y_to_brightness[1],
            )

    def display_update(self):
        current = time.localtime()
        time_text = "{:02d}:{:02d}:{:02d}".format(
            current.tm_hour, current.tm_min, current.tm_sec
        )
        self.text_area.text = time_text

    def main_loop(self):
        self.fx_extra_update()

        self.offset_update()

        # self.rainbow_update()
        self.plasma_update()
        # self.nightlight_update()

        self.handle_brightness_mask()
        self.pixels.show()

        self.display_update()
